daviinacio/white_led_digital_clock/firmware2/src/drivers/Panel.hpp

#ifndef WLDC_PANEL_H
#define WLDC_PANEL_H
#include "lib/Input.hpp"

#define PANEL_DEFAULT_INTERVAL 100
#define PANEL_DEFAULT_COOLDOWN 250

#define PANEL_RANGE_KEY_HOME        (value < 190)                   // ~0
#define PANEL_RANGE_KEY_VALUE_UP    (value >= 750 && value < 900)   // ~808
#define PANEL_RANGE_KEY_VALUE_DOWN  (value >= 550 && value < 750)   // ~651
#define PANEL_RANGE_KEY_FUNC_LEFT   (value >= 400 && value < 550)   // ~438
#define PANEL_RANGE_KEY_FUNC_RIGHT  (value >= 190 && value < 400)   // ~205

class AnalogPanel : public Input {
protected:
  unsigned short pin;

public:
  AnalogPanel(unsigned short _pin);
  AnalogPanel(unsigned short _pin, unsigned long _interval);
  AnalogPanel(unsigned short _pin, unsigned long _interval, unsigned short _cooldown);

  InputKey readInput() override;
};

// Implementation
AnalogPanel::AnalogPanel(unsigned short _pin, unsigned long _interval, unsigned short _cooldown) : Input(_interval, _cooldown) {
  pin = _pin;
}

AnalogPanel::AnalogPanel(unsigned short _pin, unsigned long _interval) : AnalogPanel(_pin, _interval, PANEL_DEFAULT_COOLDOWN) {}
AnalogPanel::AnalogPanel(unsigned short _pin) : AnalogPanel(_pin, PANEL_DEFAULT_INTERVAL, PANEL_DEFAULT_COOLDOWN){}

InputKey AnalogPanel::readInput() {
  InputKey key = KEY_DEFAULT;
  unsigned int value = analogRead(pin);

  if(PANEL_RANGE_KEY_HOME) key = KEY_HOME;
  else if(PANEL_RANGE_KEY_VALUE_UP) key = KEY_VALUE_UP;
  else if(PANEL_RANGE_KEY_VALUE_DOWN) key = KEY_VALUE_DOWN;
  else if(PANEL_RANGE_KEY_FUNC_LEFT) key = KEY_FUNC_LEFT;
  else if(PANEL_RANGE_KEY_FUNC_RIGHT) key = KEY_FUNC_RIGHT;
  
  return key;
}

AnalogPanel panel = AnalogPanel(A3, 100);

#endif
